sporkus/smol_mantis/stl/carriage_mgn9.stl

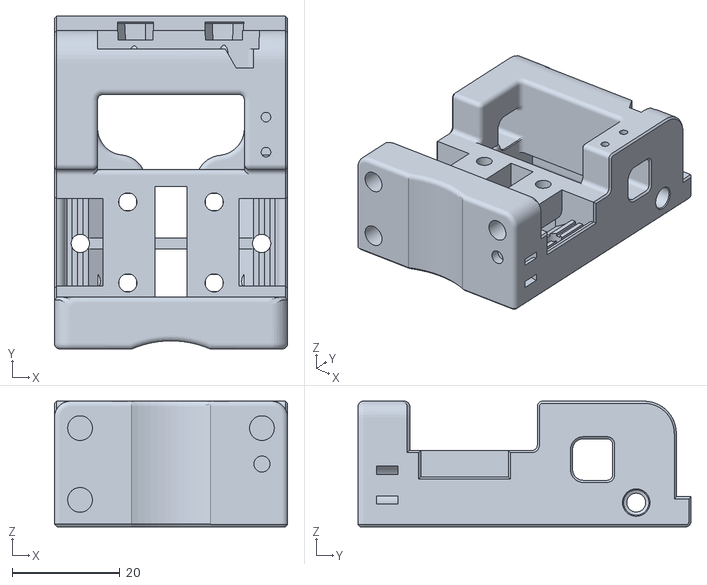
[picture p17: CAD file, 2022-08-16]
stl/carriage_mgn9.stl
43.2 x 61.7 x 23.3
