sporkus/smol_mantis/stl/4010_duct_rhs.stl

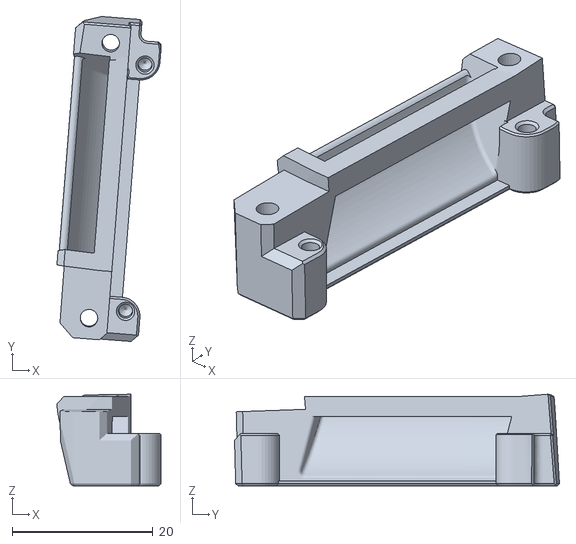
[picture p18: CAD file, 2022-08-16]
stl/4010_duct_rhs.stl
14.8 x 46.2 x 13.0
