sporkus/smol_mantis/stl/klickyNG_cap.stl

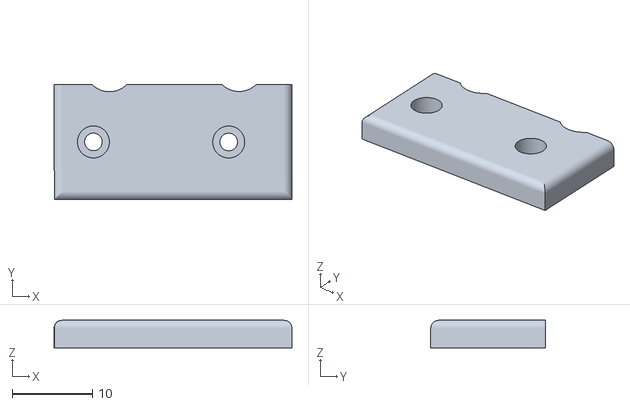
[picture p19: CAD file, 2022-07-28]
stl/klickyNG_cap.stl
29.7 x 14.3 x 3.44
