sporkus/smol_mantis/stl/klickyNG_gantry_mount.stl

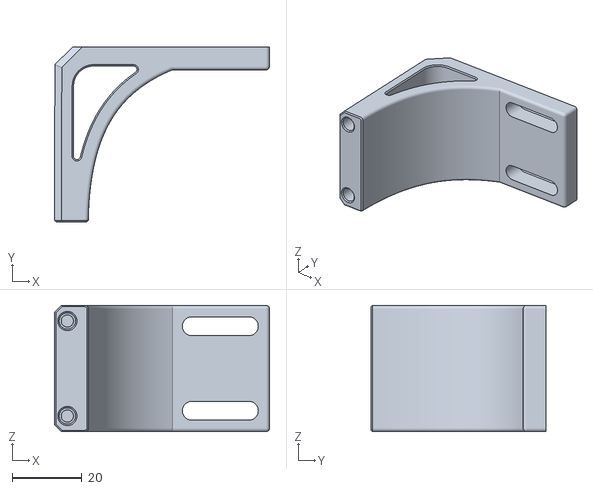
[picture p20: CAD file, 2022-07-28]
stl/klickyNG_gantry_mount.stl
61.7 x 50.1 x 36.3
